leoole100/PhasedArray/sim/res/air/1.0Spiral2Sym16.png

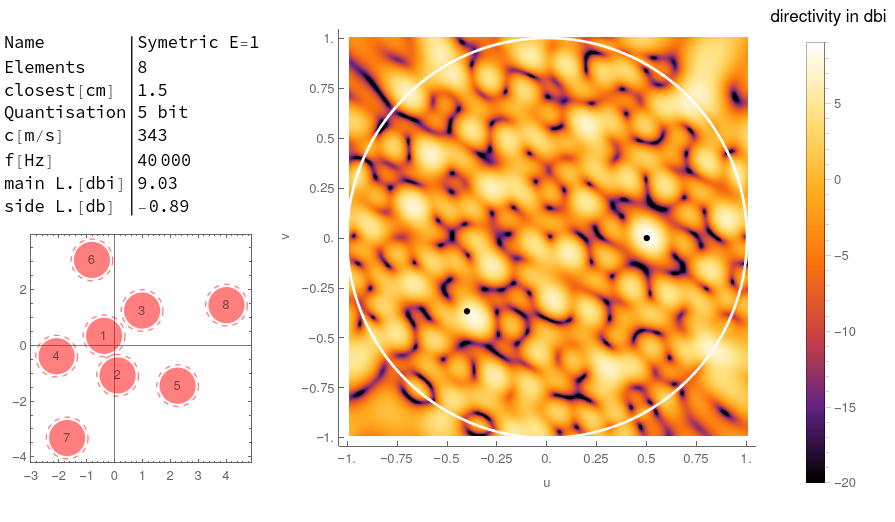
sim/res/air/1.0Spiral2Sym16.png
