leoole100/PhasedArray/sim/res/air/1.25Spiral32.png

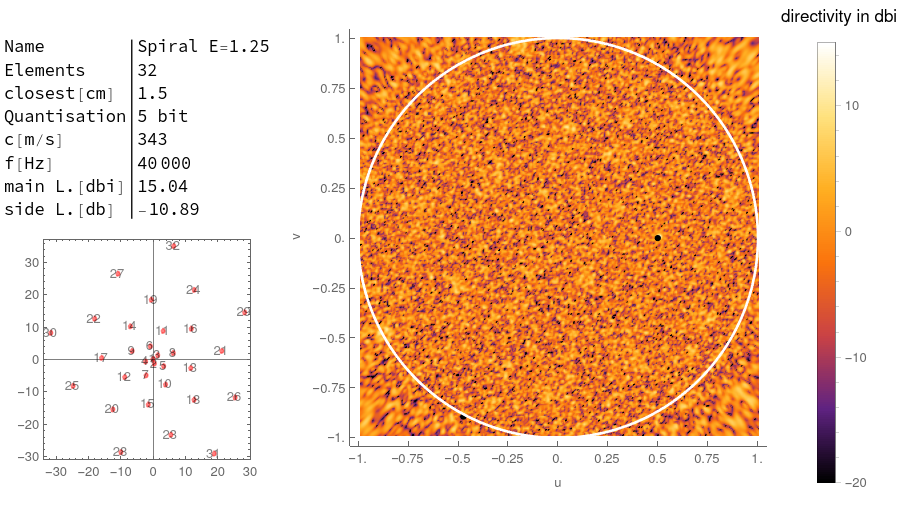
sim/res/air/1.25Spiral32.png
